quasiengineer/iapx432-sbc/gateware/top/top.v

module top (
    input         CLK_250,

    // SRAM interface
    inout  [15:0] SRAM_D,
    output [15:0] SRAM_A,
    output        SRAM_STROBE,
    output        SRAM_WR,
    output        SRAM_OE,
    output        SRAM_CLK,

    // GDP interface
    input         BOUT,
    input         FATAL,
    input         PRQ,
    output        PCLK,
    output        CLR,
    output        INIT,
    output        ICS,
    output        CLKA,
    output        CLKB,
    output        ACD_DIRECTION,
    inout [15:0]  ACD,

    input         UART_RX,
    output        UART_TX,
    output        LED
);

  localparam integer WRITE_LOG_ADDR_WIDTH = 7;
  localparam integer BUS_LOG_ADDR_WIDTH = 12;

  // clock generation
  wire clk_50, clk_125;
  wire clka, clkb;
  wire rst_n;
  clock_gen u_clock_gen (
    .clk_250(CLK_250),
    .clk_125(clk_125),
    .clk_50(clk_50),
    .rst_n(rst_n),
    .clka(clka),
    .clkb(clkb)
  );
  assign CLKA = clka;
  assign CLKB = clkb;

  // SRAM should work at 125Mhz
  wire sram_ctrl_clk;
  assign sram_ctrl_clk = clk_125;

  // LED flickering
  reg [24:0] counter;
  always @(posedge clk_50) counter <= counter + 1;
  assign LED = ~counter[24];

  // PCLK/ generator (0.1 Hz, active-low pulse)
  localparam integer PCLK_DIV = 50000000; // 5 MHz / 50000000 = 0.1 Hz
  reg [25:0] pclk_div;
  reg pclk_n;
  always @(posedge clka or negedge rst_n) begin
    if (!rst_n) begin
      pclk_div <= 26'd0;
      pclk_n   <= 1'b1;
    end
    else begin
      if (pclk_div == PCLK_DIV - 1) pclk_div <= 26'd0;
      else pclk_div <= pclk_div + 1'b1;
      pclk_n <= (pclk_div == 26'd0) ? 1'b0 : 1'b1;
    end
  end
  assign PCLK = pclk_n;

  // access log storage
  wire [BUS_LOG_ADDR_WIDTH-1:0]  u_log_addr;
  wire [23:0] u_log_data_in;
  wire [23:0] u_log_data_out;
  wire u_log_wr, u_log_rd, u_log_data_valid;
  wire log_wr;
  wire [7:0] log_type;
  wire [15:0] log_addr;
  wire [BUS_LOG_ADDR_WIDTH-1:0] log_wr_ptr;
  execution_log #(
    .ADDR_WIDTH(BUS_LOG_ADDR_WIDTH)
  ) log_storage (
    .clk(clk_50),
    .rst_n(rst_n),
    .u_addr(u_log_addr),
    .u_data_in(u_log_data_in),
    .u_wr(u_log_wr),
    .u_rd(u_log_rd),
    .u_data_out(u_log_data_out),
    .u_data_valid(u_log_data_valid),
    .log_write_clk(clkb),
    .log_wr(log_wr),
    .log_type(log_type),
    .log_addr(log_addr),
    .log_wr_ptr(log_wr_ptr),
    .trigger_init(gdp_trigger_init)
  );

  // write log storage
  wire [WRITE_LOG_ADDR_WIDTH-1:0]  u_wlog_addr;
  wire [32:0] u_wlog_data_out;
  wire u_wlog_rd;
  wire wlog_wr;
  wire [15:0] wlog_data;
  wire [15:0] wlog_addr;
  write_log #(
    .ADDR_WIDTH(WRITE_LOG_ADDR_WIDTH)
  ) wlog_storage (
    .clk(clk_50),
    .rst_n(rst_n),
    .u_addr(u_wlog_addr),
    .u_rd(u_wlog_rd),
    .u_data_out(u_wlog_data_out),
    .log_write_clk(clkb),
    .log_wr(wlog_wr),
    .log_data(wlog_data),
    .log_addr(wlog_addr),
    .trigger_init(gdp_trigger_init)
  );

  // ====================================================================================================
  // UART control module (50Mhz) -> CDC bridge -> SRAM mux port 0 (125 Mhz) -> SRAM controller (125 Mhz)
  // GDP memory controller (5Mhz) -> CDC bridge -> SRAM mux port 1 (125 Mhz) -> SRAM controller (125 Mhz)
  // ====================================================================================================

  // SRAM multiplexer ports
  wire sram_req0, sram_req1;
  wire sram_wr0, sram_wr1;
  wire sram_rd0, sram_rd1;
  wire [15:0] sram_addr0;
  wire [15:0] sram_addr1;
  wire [15:0] sram_wdata0;
  wire [15:0] sram_wdata1;
  // SRAM multiplexer generic outputs
  wire [15:0] sram_rdata;
  wire sram_valid;
  wire sram_busy;

  // SRAM signals for UART control module
  wire sram_u_req;
  wire sram_u_wr;
  wire sram_u_rd;
  wire [15:0] sram_u_addr;
  wire [15:0] sram_u_wdata;
  wire [15:0] sram_u_rdata;
  wire sram_u_valid;
  wire sram_u_busy;

  // SRAM signals for GDP memory controller
  wire sram_g_req;
  wire sram_g_wr;
  wire sram_g_rd;
  wire [15:0] sram_g_addr;
  wire [15:0] sram_g_wdata;
  wire [15:0] sram_g_rdata;

  sram_mux sram_ctrl (
    .clk(sram_ctrl_clk),
    .rst_n(rst_n),
    .req0(sram_req0),
    .wr0(sram_wr0),
    .rd0(sram_rd0),
    .addr0(sram_addr0),
    .wdata0(sram_wdata0),
    .req1(sram_req1),
    .wr1(sram_wr1),
    .rd1(sram_rd1),
    .addr1(sram_addr1),
    .wdata1(sram_wdata1),
    .rdata(sram_rdata),
    .valid(sram_valid),
    .busy(sram_busy),
    .sram_addr_io(SRAM_A),
    .sram_data_io(SRAM_D),
    .sram_we_n_io(SRAM_WR),
    .sram_oe_n_io(SRAM_OE),
    .sram_adsc_n_io(SRAM_STROBE),
    .sram_clk_io(SRAM_CLK)
  );

  // CDC bridge from 50 MHz control to 125 MHz SRAM (port0)
  sram_cdc_bridge sram_uart_cdc (
    .tgt_clk(clk_50),
    .tgt_rst_n(rst_n),
    .tgt_req(sram_u_req),
    .tgt_wr_req(sram_u_wr),
    .tgt_rd_req(sram_u_rd),
    .tgt_addr(sram_u_addr),
    .tgt_wdata(sram_u_wdata),
    .tgt_rdata(sram_u_rdata),
    .tgt_done(sram_u_valid),
    .tgt_busy(sram_u_busy),
    .s_clk(sram_ctrl_clk),
    .s_rst_n(rst_n),
    .s_req(sram_req0),
    .s_wr_req(sram_wr0),
    .s_rd_req(sram_rd0),
    .s_addr(sram_addr0),
    .s_wdata(sram_wdata0),
    .s_rdata(sram_rdata),
    .s_valid(sram_valid)
  );

  wire [7:0] uart_tx_ctrl_data;
  wire uart_tx_ctrl_req;
  wire [7:0] uart_tx_gdp_data;
  wire uart_tx_gdp_req;
  wire uart_tx_busy;
  uart_tx_mux uart_mux (
    .uart_clk(clk_50),
    .rst_n(rst_n),
    .data0(uart_tx_ctrl_data),
    .req0(uart_tx_ctrl_req),
    .data1(uart_tx_gdp_data),
    .req1(uart_tx_gdp_req),
    .tx_busy(uart_tx_busy),
    .uart_tx_io(UART_TX)
  );

  control_interface #(
    .WRITE_LOG_ADDR_WIDTH(WRITE_LOG_ADDR_WIDTH),
    .BUS_LOG_ADDR_WIDTH(BUS_LOG_ADDR_WIDTH)
  ) control_interface (
    .clk(clk_50),
    .rst_n(rst_n),
    .uart_rx_io(UART_RX),
    .uart_tx_data(uart_tx_ctrl_data),
    .uart_tx_req(uart_tx_ctrl_req),
    .uart_tx_busy(uart_tx_busy),
    .sram_req(sram_u_req),
    .sram_wr(sram_u_wr),
    .sram_rd(sram_u_rd),
    .sram_addr(sram_u_addr),
    .sram_rdata(sram_u_rdata),
    .sram_wdata(sram_u_wdata),
    .sram_busy(sram_u_busy),
    .sram_data_valid(sram_u_valid),
    .u_log_addr(u_log_addr),
    .u_log_data_in(u_log_data_in),
    .u_log_data_out(u_log_data_out),
    .u_log_data_valid(u_log_data_valid),
    .u_log_wr(u_log_wr),
    .u_log_rd(u_log_rd),
    .u_wlog_addr(u_wlog_addr),
    .u_wlog_rd(u_wlog_rd),
    .u_wlog_data_out(u_wlog_data_out),
    .gdp_trigger_init(gdp_trigger_init)
  );

  // CDC bridge from 5 MHz GDP to 125 MHz SRAM (port0), it's faster CDC because it doesn't work on slow clock at all
  //   it assumes that GDP clock is derived from 125 MHz clock, so we can avoid FF synchronization
  sram_gdp_cdc_bridge sram_gdp_cdc (
    .gdp_req(sram_g_req),
    .gdp_wr_req(sram_g_wr),
    .gdp_rd_req(sram_g_rd),
    .gdp_addr(sram_g_addr),
    .gdp_wdata(sram_g_wdata),
    .gdp_rdata(sram_g_rdata),
    .s_clk(sram_ctrl_clk),
    .s_rst_n(rst_n),
    .s_req(sram_req1),
    .s_wr_req(sram_wr1),
    .s_rd_req(sram_rd1),
    .s_addr(sram_addr1),
    .s_wdata(sram_wdata1),
    .s_rdata(sram_rdata),
    .s_valid(sram_valid)
  );

  // GDP wiring
  reg gdp_trigger_init;
  gdp_interface #(
    .BUS_LOG_ADDR_WIDTH(BUS_LOG_ADDR_WIDTH)
  ) gdp (
    .u_clk(clk_50),
    .rst_n(rst_n),
    .led_io(LED),
    .clka(clka),
    .clkb(clkb),
    .bout_io(BOUT),
    .fatal_io(FATAL),
    .prq_io(PRQ),
    .acd_io(ACD),
    .acd_direction_io(ACD_DIRECTION),
    .clr_io(CLR),
    .init_io(INIT),
    .ics_io(ICS),
    .uart_send(uart_tx_gdp_req),
    .uart_data(uart_tx_gdp_data),
    .uart_busy(uart_tx_busy),
    .sram_req(sram_g_req),
    .sram_wr(sram_g_wr),
    .sram_rd(sram_g_rd),
    .sram_addr(sram_g_addr),
    .sram_rdata(sram_g_rdata),
    .sram_wdata(sram_g_wdata),
    .log_wr(log_wr),
    .log_type(log_type),
    .log_addr(log_addr),
    .log_wr_ptr(log_wr_ptr),
    .wlog_wr(wlog_wr),
    .wlog_data(wlog_data),
    .wlog_addr(wlog_addr),
    .trigger_init(gdp_trigger_init)
  );

endmodule
