quasiengineer/iapx432-sbc/gateware/rtl/sram_gdp_cdc_bridge.v

module sram_gdp_cdc_bridge (
  // GDP Domain (slow)
  input  wire        gdp_req,
  input  wire        gdp_wr_req,  // Pulse
  input  wire        gdp_rd_req,  // Pulse
  input  wire [15:0] gdp_addr,
  input  wire [15:0] gdp_wdata,
  output wire [15:0] gdp_rdata,

  // SRAM Domain (fast)
  input  wire        s_clk,
  input  wire        s_rst_n,
  output reg         s_req,
  output reg         s_wr_req,  // Pulse
  output reg         s_rd_req,  // Pulse
  output reg  [15:0] s_addr,
  output reg  [15:0] s_wdata,
  input  wire [15:0] s_rdata,
  input  wire        s_valid    // Pulse
);

  // regular 2-FF synchronizer for gdp_req
  reg req_sync0, req_sync1;
  always @(posedge s_clk or negedge s_rst_n) begin
    if (!s_rst_n) begin
      s_req <= 0;
    end
    else begin
      req_sync0 <= gdp_req;
      req_sync1 <= req_sync0;
      s_req <= req_sync1;
    end
  end

  // Synchronize inputs to fast clock domain
  reg [15:0] gdp_addr_sync1, gdp_addr_sync2;
  reg gdp_wr_sync1, gdp_wr_sync2;
  reg gdp_rd_sync1, gdp_rd_sync2;
  reg [15:0] gdp_wdata_sync1, gdp_wdata_sync2;

  always @(posedge s_clk or negedge s_rst_n) begin
    if (~s_rst_n) begin
      gdp_addr_sync1 <= 0;
      gdp_addr_sync2 <= 0;
      gdp_wr_sync1 <= 0;
      gdp_wr_sync2 <= 0;
      gdp_rd_sync1 <= 0;
      gdp_rd_sync2 <= 0;
      gdp_wdata_sync1 <= 0;
      gdp_wdata_sync2 <= 0;
    end
    else begin
      gdp_addr_sync1 <= gdp_addr;
      gdp_addr_sync2 <= gdp_addr_sync1;
      gdp_wr_sync1 <= gdp_wr_req;
      gdp_wr_sync2 <= gdp_wr_sync1;
      gdp_rd_sync1 <= gdp_rd_req;
      gdp_rd_sync2 <= gdp_rd_sync1;
      gdp_wdata_sync1 <= gdp_wdata;
      gdp_wdata_sync2 <= gdp_wdata_sync1;
    end
  end

  // also need to trigger SRAM access when address is changed with active request signal
  reg trigger_sram_access_reg;
  wire trigger_sram_access =
    (gdp_wr_sync1 & ~gdp_wr_sync2)
    || (gdp_rd_sync1 & ~gdp_rd_sync2)
    || ((gdp_addr_sync2 != gdp_addr_sync1) & (gdp_wr_sync2 | gdp_rd_sync2));

  always @(posedge s_clk or negedge s_rst_n) begin
      if (~s_rst_n) trigger_sram_access_reg <= 0;
      else          trigger_sram_access_reg <= trigger_sram_access;
  end

  reg [15:0] data_out_int;
  reg is_read;

  always @(posedge s_clk or negedge s_rst_n) begin
    if (~s_rst_n) begin
      data_out_int <= 0;
      s_wr_req <= 0;
      s_rd_req <= 0;
      s_addr <= 0;
      s_wdata <= 0;
    end
    else begin
      s_wr_req <= 0;
      s_rd_req <= 0;

      if (trigger_sram_access_reg) begin
        s_addr <= gdp_addr_sync1;
        s_wr_req <= gdp_wr_sync2;
        s_rd_req <= gdp_rd_sync2;
        s_wdata <= gdp_wdata_sync2;
        is_read <= gdp_rd_sync2;
      end

      if (is_read && s_valid) begin
        data_out_int <= s_rdata;
      end
    end
  end

  // Directly use fast domain signals in slow domain (assuming synchronous domains)
  assign gdp_rdata = data_out_int;
endmodule
